Vtechcode/IoT_E-bike_Charger/Images/control-3d.jpg

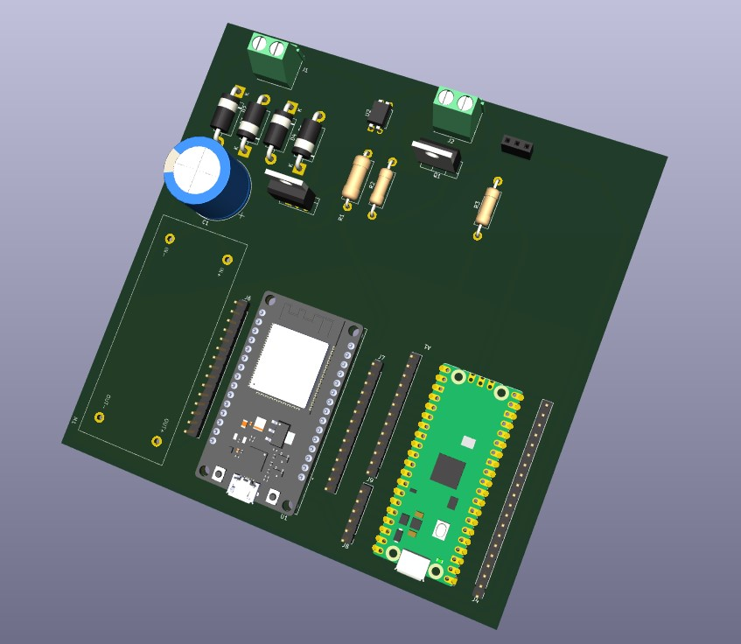
Images/control-3d.jpg
