Vtechcode/IoT_E-bike_Charger/Images/control-bottom.jpg

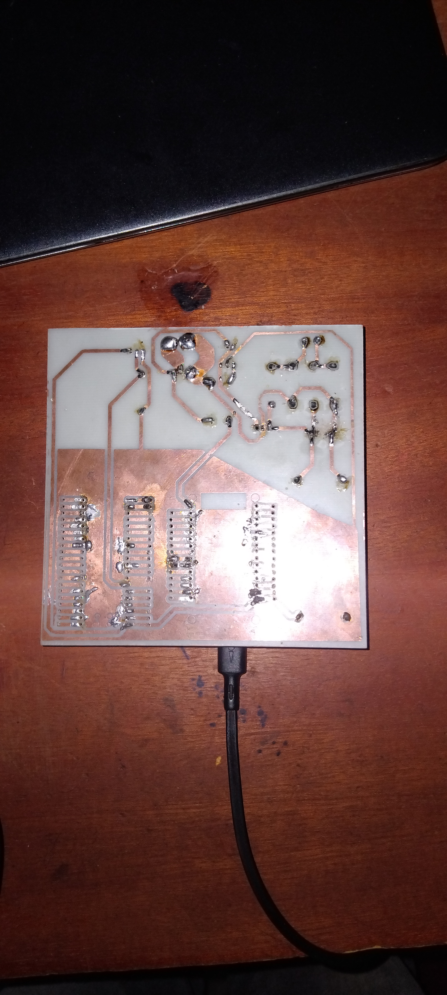
Images/control-bottom.jpg
