Vtechcode/IoT_E-bike_Charger/Images/control-layout.jpg

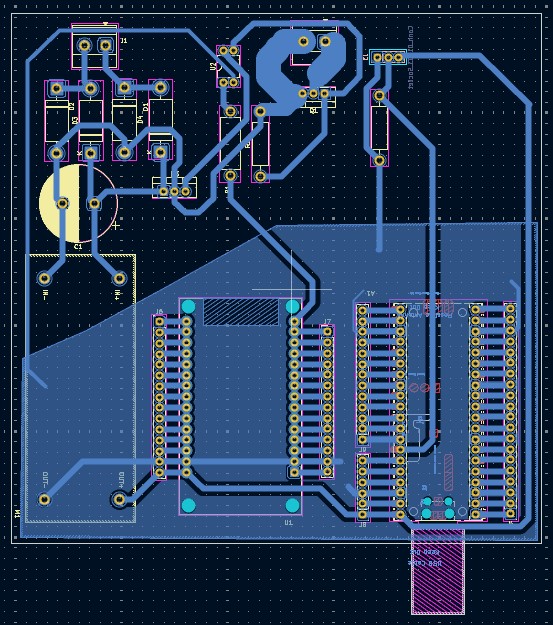
Images/control-layout.jpg
