Vtechcode/IoT_E-bike_Charger/Images/Final-product.jpg

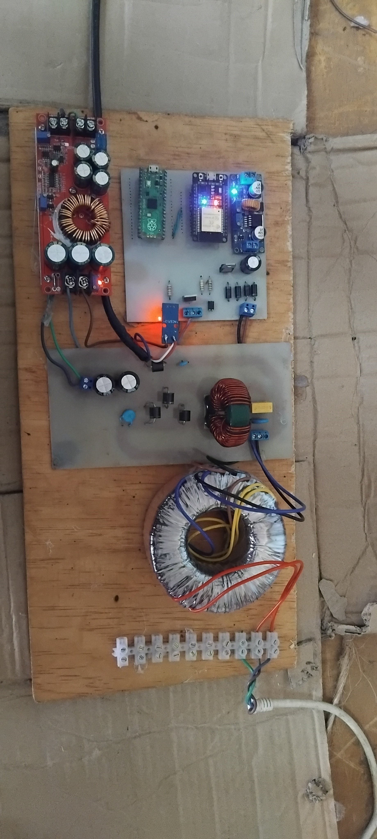
Images/Final-product.jpg
