Vtechcode/IoT_E-bike_Charger/Images/IMG_20251222_093929.jpg

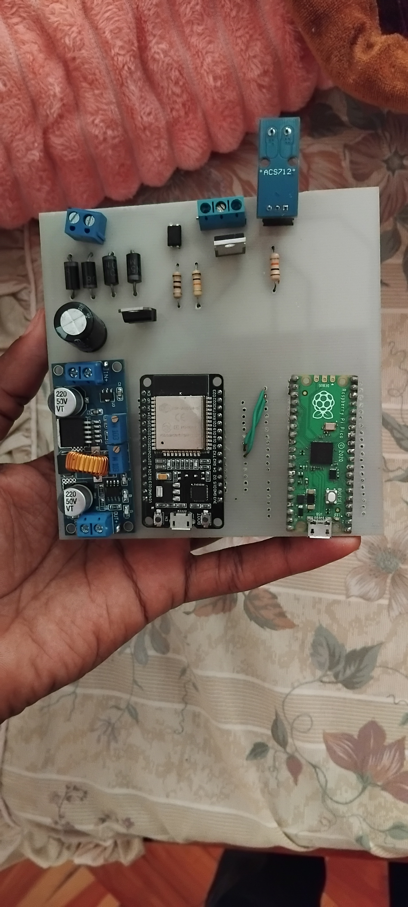
Images/IMG_20251222_093929.jpg
