Vtechcode/IoT_E-bike_Charger/Images/IMG_20260106_151534.jpg

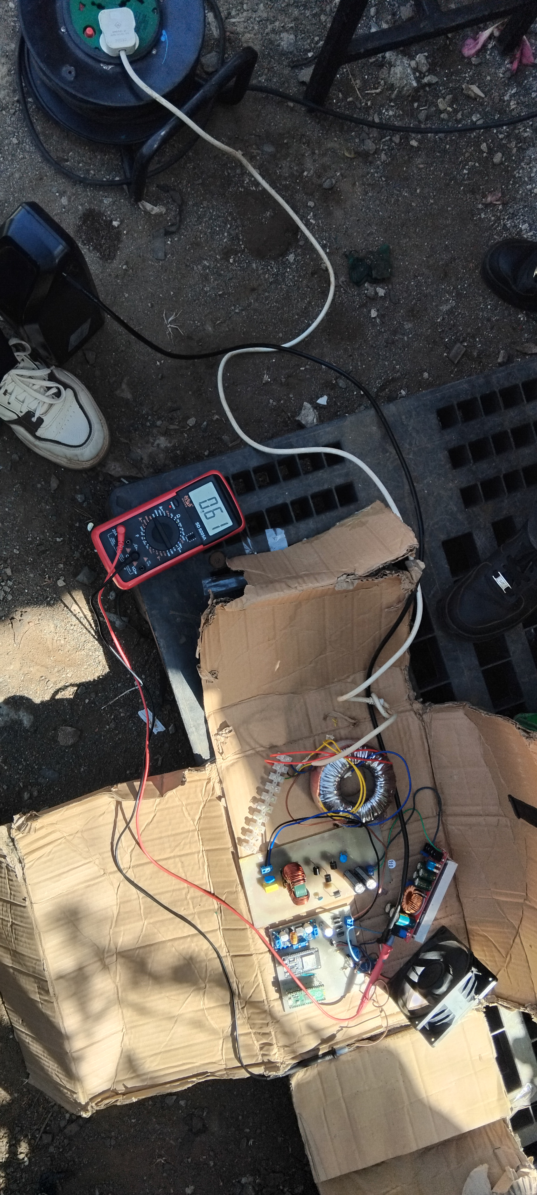
Images/IMG_20260106_151534.jpg
