Vtechcode/IoT_E-bike_Charger/Images/IMG_20260121_140934.jpg

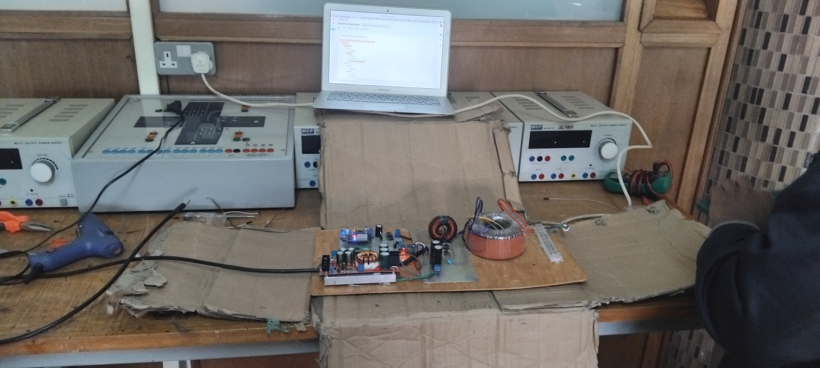
Images/IMG_20260121_140934.jpg
