Vtechcode/IoT_E-bike_Charger/Images/multimeter-reading.jpg

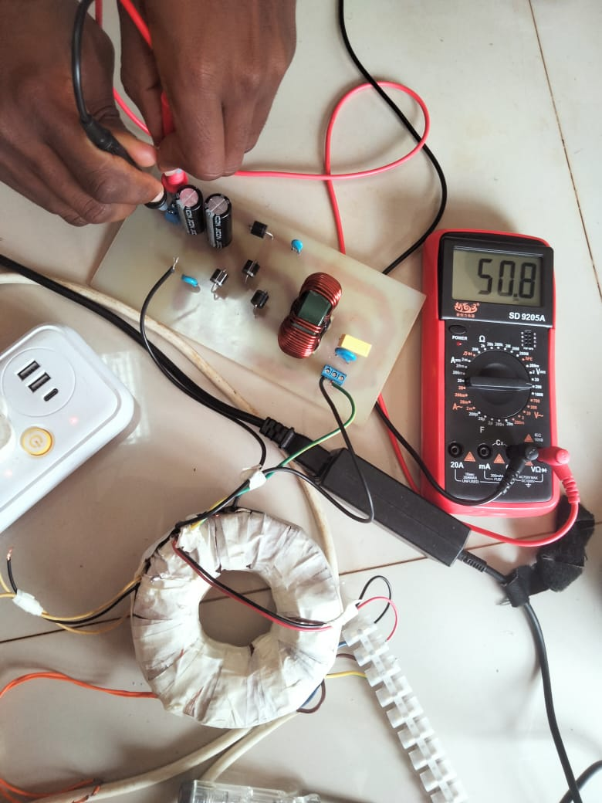
Images/multimeter-reading.jpg
