Vtechcode/IoT_E-bike_Charger/Images/rectification-3d.png

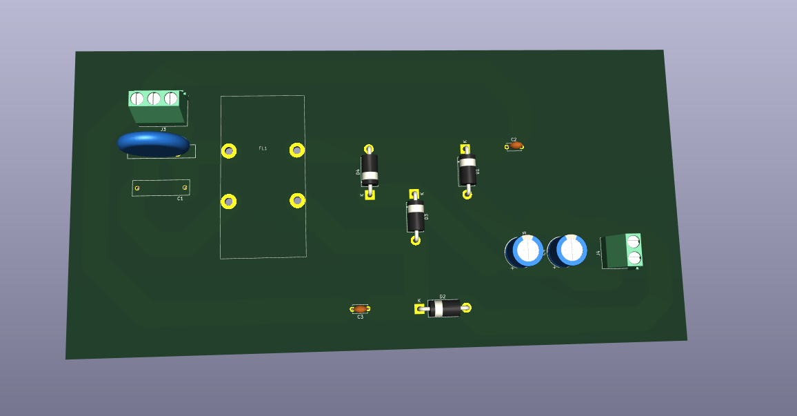
Images/rectification-3d.png
