Vtechcode/IoT_E-bike_Charger/Images/rectification-bottom.jpg

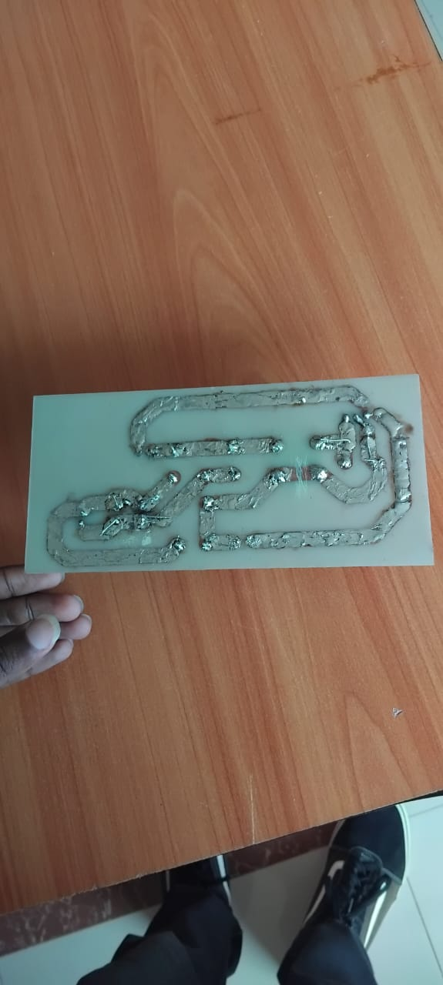
Images/rectification-bottom.jpg
