Vtechcode/IoT_E-bike_Charger/Images/rectification-layout.png

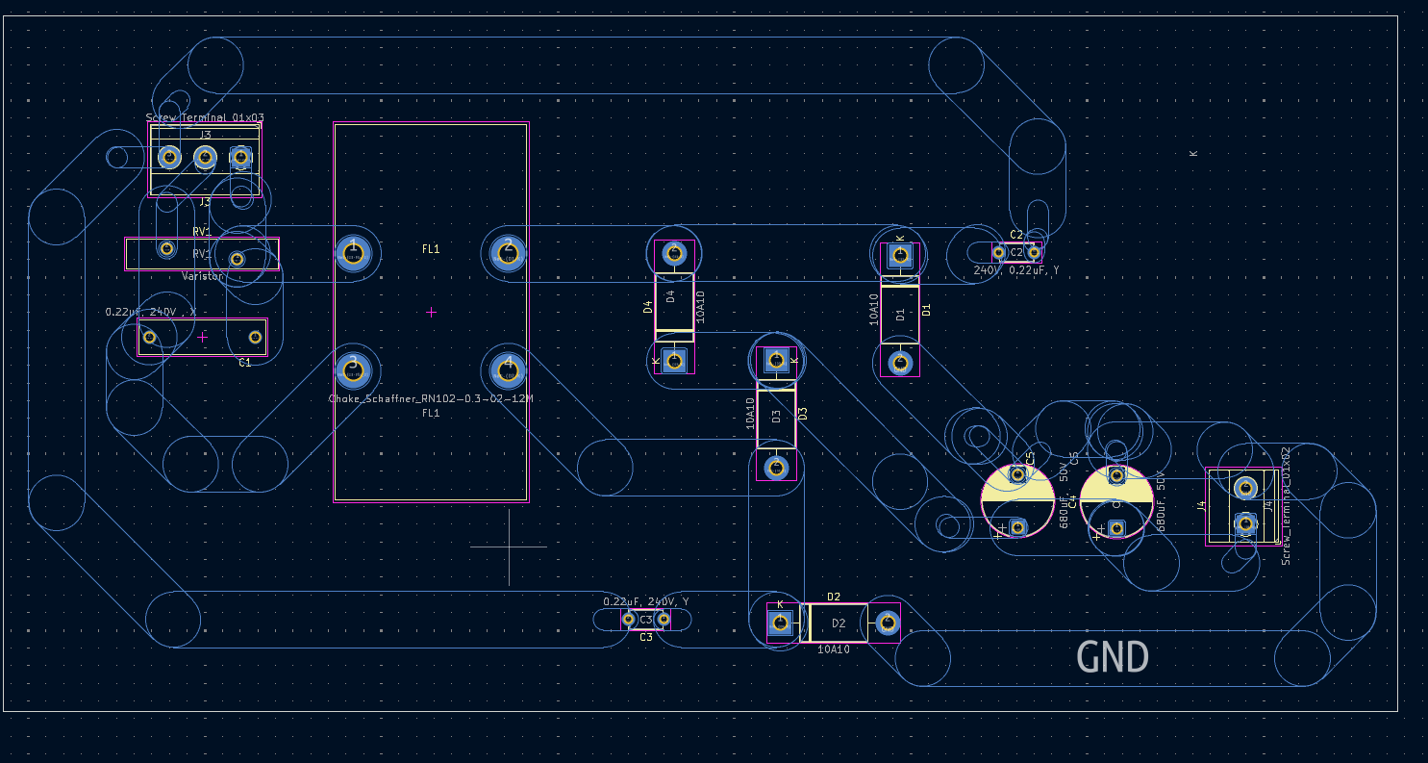
Images/rectification-layout.png
