Vtechcode/IoT_E-bike_Charger/Images/rectification-top.jpg

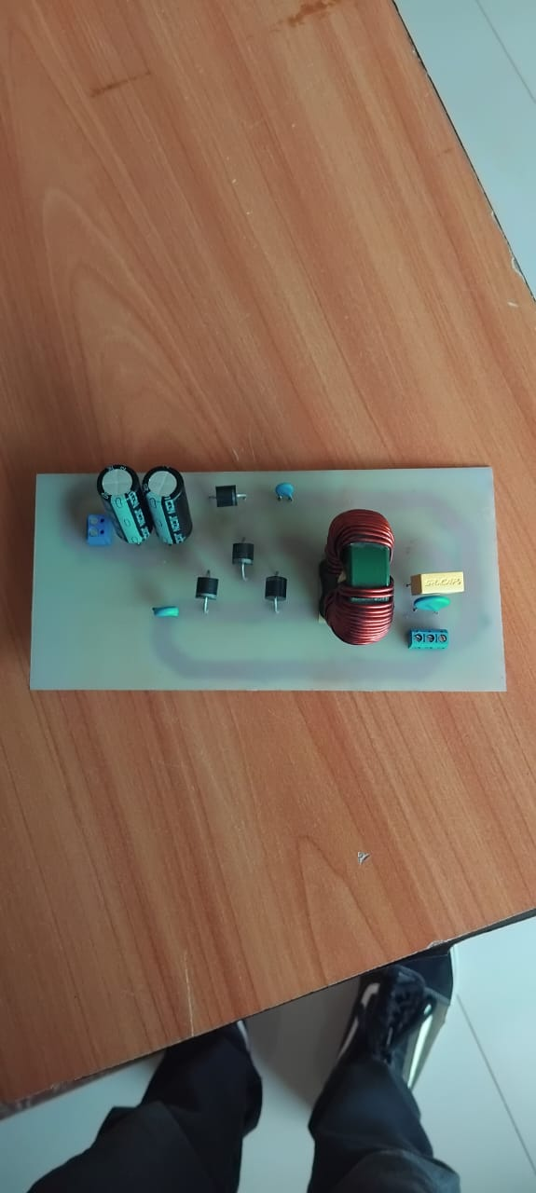
Images/rectification-top.jpg
