Vtechcode/IoT_E-bike_Charger/Images/settings.jpeg

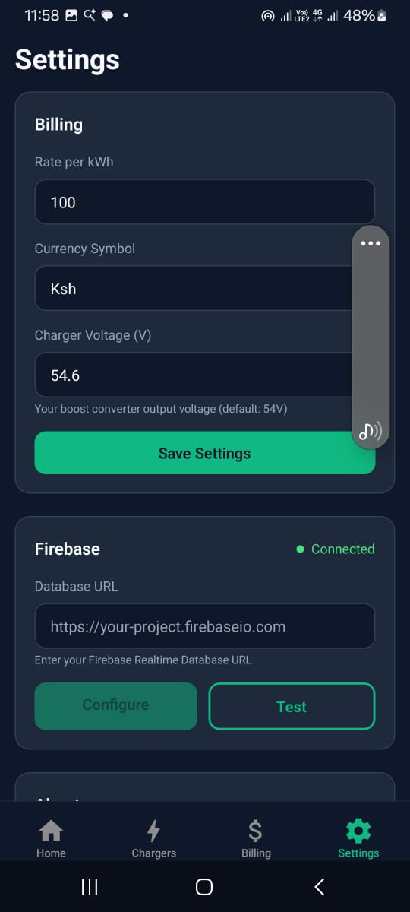
Images/settings.jpeg
