Vtechcode/IoT_E-bike_Charger/Images/test1.jpg

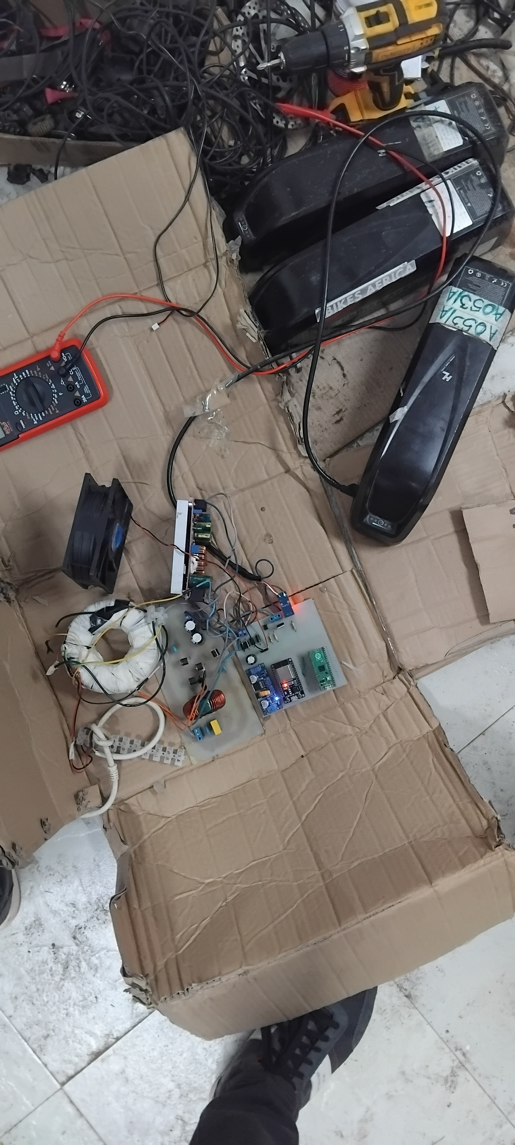
Images/test1.jpg
