Vtechcode/IoT_E-bike_Charger/Images/test-final.jpg

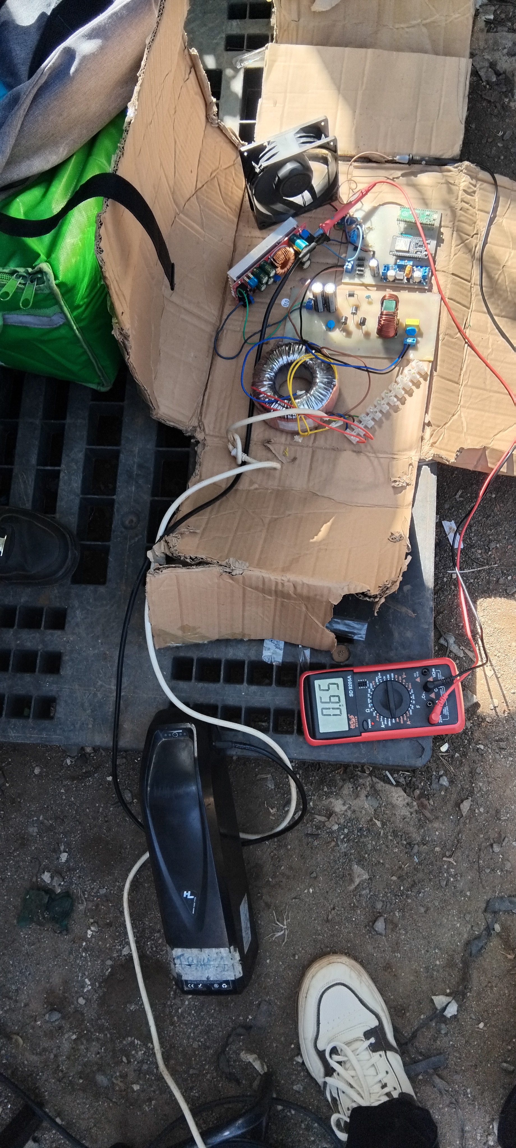
Images/test-final.jpg
